chrisnovello/illucia_dtr/illuciaConnect/data/illuciaConnected.png

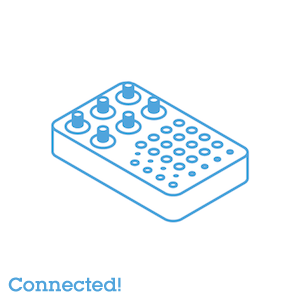
illuciaConnect/data/illuciaConnected.png
